NNNILabs/Discrete-Linear-Power-Supply/simulations/Draft30.asc

C1: cap; 10µF
C2: cap; 100pF
C3: cap; 470nF
E1: e; 1
I1: current; 6mA
M1: pmos; IRFP9240
Q1: npn; 2N5550
Q2: npn; 2N5550
Q3: pnp; 2N5401
Q4: pnp; 2N5401
Q5: pnp; 2N5401
Q6: pnp; 2N5401
Q7: npn; 2N5550
R1: res; 56
R2: res; 56
R3: res; 56
R4: res; 1K
R5: res; 1K
R6: res; 0.1
R7: res; 56
V1: voltage; 50
V2: voltage; ""; AC 1
Named nets: 0, in, out
.ac dec 100 1 100Meg
;.step param C list 1uF 10uF 100uF 1000uF
;.step param R list 1 1K 2.5K 5K
